GlassyBridge/Keyboard/PCB/3d models/SS34.step

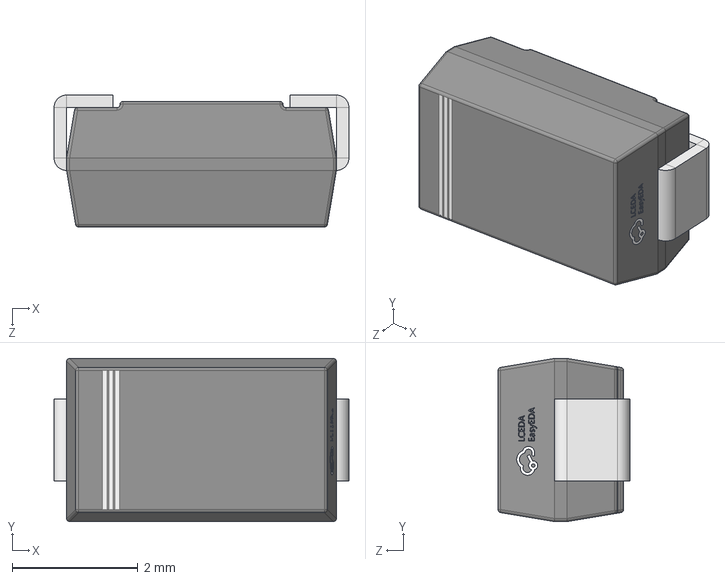
[picture p15: CAD file, 2026-02-24]
PCB/3d models/SS34.step
4.70 x 2.60 x 2.10 mm
