GlassyBridge/Keyboard/PCB/3d models/TYPE-C-31-M-12--3DModel-STEP-56544.STEP

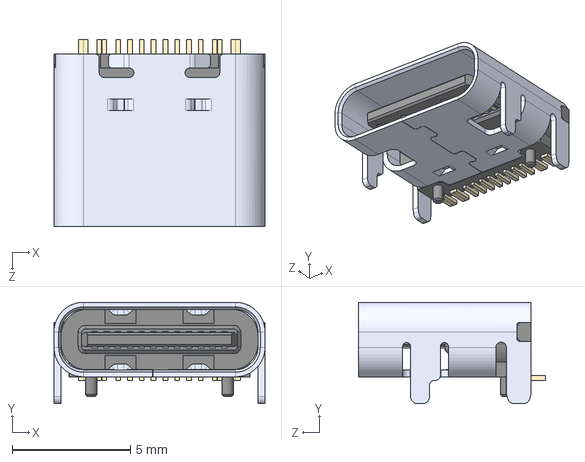
[picture p16: CAD file, 2026-02-11]
PCB/3d models/TYPE-C-31-M-12--3DModel-STEP-56544.STEP
8.94 x 4.30 x 7.90 mm
