GlassyBridge/Keyboard/PCB/3d models/OLED-128x64-0.96.step

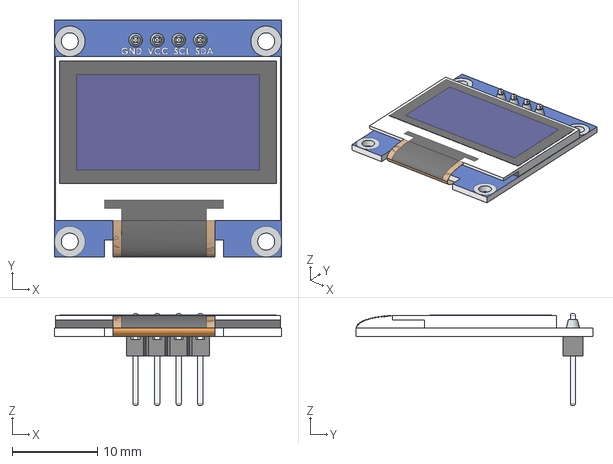
[picture p17: CAD file, 2026-02-11]
PCB/3d models/OLED-128x64-0.96.step
26.7 x 27.9 x 10.8 mm
