GlassyBridge/Keyboard/PCB/3d models/XIAO-nRF52840 v15.step

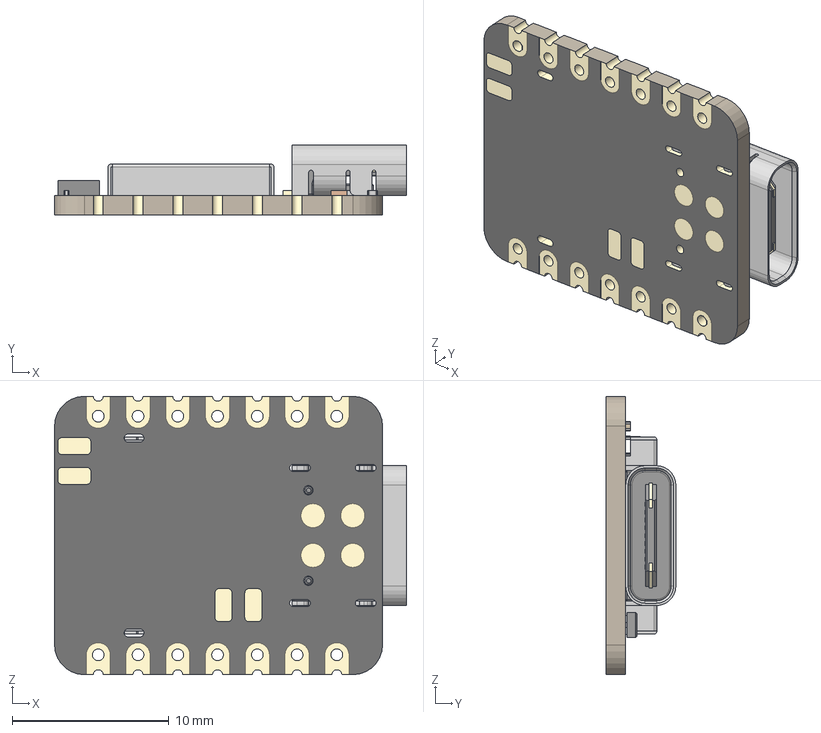
[picture p18: CAD file, 2026-02-11]
PCB/3d models/XIAO-nRF52840 v15.step
22.5 x 4.46 x 17.8 mm
BOSS-EXTRUDE14_8_
BOSS-EXTRUDE7_4_
BOSS-EXTRUDE7_3_
BOSS-EXTRUDE14_4_
BOSS-EXTRUDE14_2_
BOSS-EXTRUDE14_11_
BOSS-EXTRUDE7_7_
BOSS-EXTRUDE14_9_
BOSS-EXTRUDE14_3_
BOSS-EXTRUDE14_7_
MIRROR2
BOSS-EXTRUDE14_5_
BOSS-EXTRUDE14_12_
BOSS-EXTRUDE7_8_
BOSS-EXTRUDE7_1_
BOSS-EXTRUDE14_10_
BOSS-EXTRUDE7_9_
BOSS-EXTRUDE14_6_
BOSS-EXTRUDE14_1_
BOSS-EXTRUDE7_6_
BOSS-EXTRUDE7_2_
CUT-EXTRUDE5
BOSS-EXTRUDE7_5_
Shield
Pins
CAP x 2
ANT1
Silkscreen
CAP 3
LED
USR
2 v1
